grobique/minimal_OPNA_player/minimalOPNA.kicad_sch

## KiCad design minimalOPNA.kicad_sch (2026-03-28)

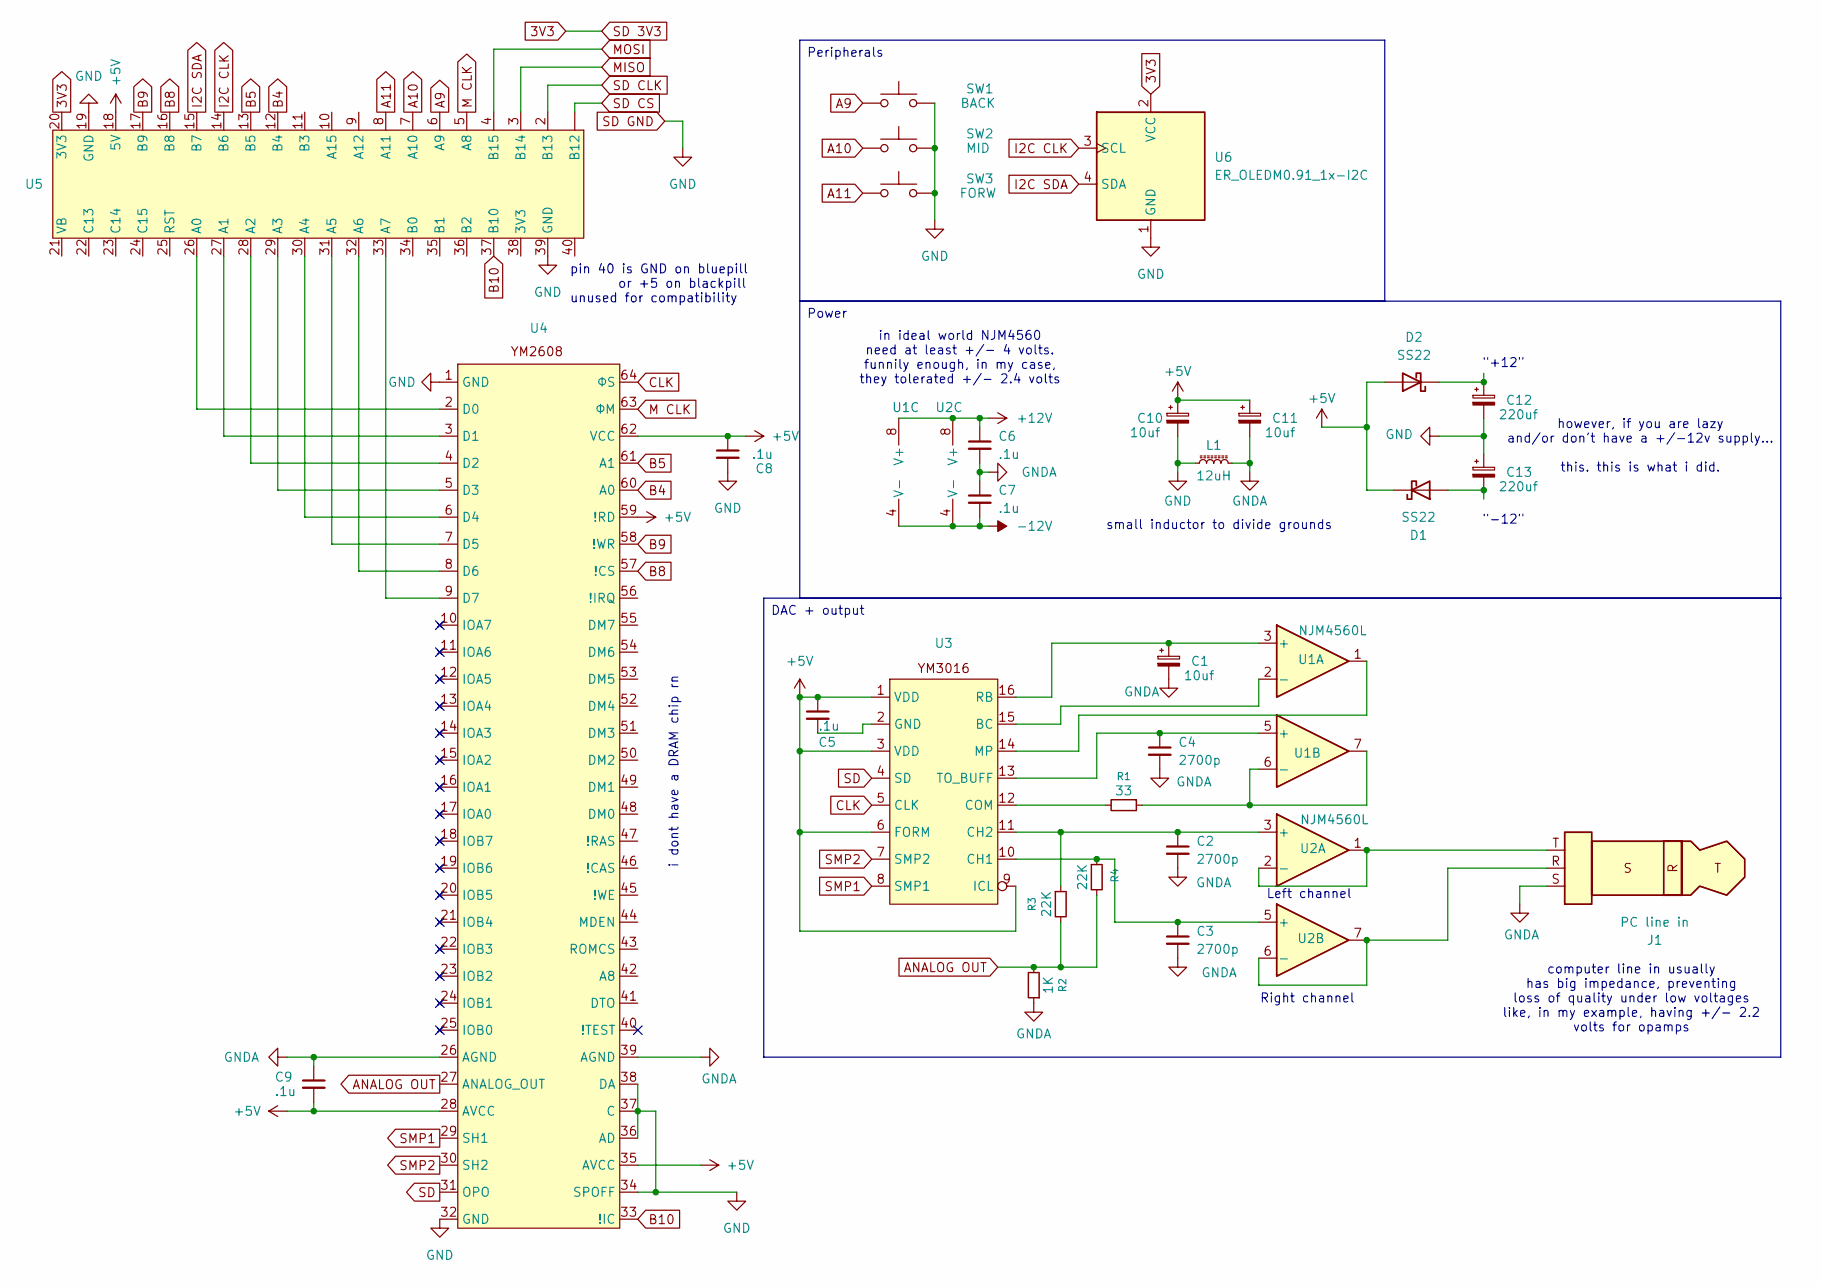
[picture p2: schematic minimalOPNA.kicad_sch]

Parts:
C1, C10, C11: 10uf
C2, C3, C4: 2700p
C5, C6, C7, C8, C9: .1u
C12, C13: 220uf
D1, D2: SS22; D_SMA
J1: PC line in
L1: 12uH
R1: 33
R2: 1K
R3, R4: 22K
SW1: BACK
SW2: MID
SW3: FORW
U1, U2: NJM4560L
U3, U4, U5: (no value)
U6: ER_OLEDM0.91_1x-I2C

Connections:
3V3: U5.20 (3V3), U6.2 (VCC)
+5V: C5.1, C8.1, C9.2, C10.1, C11.1, D1.1 (K), D2.2 (A), U3.1 (VDD), U3.3 (VDD), U3.6 (FORM), U3.9 (ICL), U4.28 (AVCC), U4.35 (AVCC), U4.59 (!RD), U4.62 (VCC), U5.18 (5V)
+12V: C6.1, U1.8 (V+), U2.8 (V+)
-12V: C7.2, U1.4 (V-), U2.4 (V-)
A9: SW1.1, U5.6 (A9)
A10: SW2.1, U5.7 (A10)
A11: SW3.1, U5.8 (A11)
ANALOG OUT: R2.2, R3.2, R4.2, U4.27 (ANALOG_OUT)
B4: U4.60 (A0), U5.12 (B4)
B5: U4.61 (A1), U5.13 (B5)
B8: U4.57 (!CS), U5.16 (B8)
B9: U4.58 (!WR), U5.17 (B9)
B10: U4.33 (!IC), U5.37 (B10)
CLK: U3.5 (CLK), U4.64 (ФS)
GND: C8.2, C10.2, C12.2, C13.1, L1.1, SW1.2, SW2.2, SW3.2, U4.1 (GND), U4.32 (GND), U4.34 (SPOFF), U4.36 (AD), U4.37 (C), U4.38 (DA), U5.19 (GND), U5.39 (GND), U6.1 (GND)
GNDA: C1.2, C2.2, C3.2, C4.2, C6.2, C7.1, C9.1, C11.2, J1.S, L1.2, R2.1, U4.26 (AGND), U4.39 (AGND)
I2C CLK: U5.14 (B6), U6.3 (SCL)
I2C SDA: U5.15 (B7), U6.4 (SDA)
M CLK: U4.63 (ФM), U5.5 (A8)
MISO: U5.3 (B14)
MOSI: U5.4 (B15)
unnamed: C1.1, U1.3 (+), U3.16 (RB)
unnamed: C2.1, R3.1, U2.3 (+), U3.11 (CH2)
unnamed: C3.1, R4.1, U2.5 (+), U3.10 (CH1)
unnamed: C4.1, U1.5 (+), U3.13 (TO_BUFF)
unnamed: C5.2, U3.2 (GND)
unnamed: C12.1, D2.1 (K)
unnamed: C13.2, D1.2 (A)
unnamed: J1.R, U2.6 (-), U2.7
unnamed: J1.T, U2.1, U2.2 (-)
unnamed: R1.1, U1.6 (-), U1.7
unnamed: R1.2, U3.12 (COM)
unnamed: U1.1, U3.14 (MP)
unnamed: U1.2 (-), U3.15 (BC)
unnamed: U4.2 (D0), U5.26 (A0)
unnamed: U4.3 (D1), U5.27 (A1)
unnamed: U4.4 (D2), U5.28 (A2)
unnamed: U4.5 (D3), U5.29 (A3)
unnamed: U4.6 (D4), U5.30 (A4)
unnamed: U4.7 (D5), U5.31 (A5)
unnamed: U4.8 (D6), U5.32 (A6)
unnamed: U4.9 (D7), U5.33 (A7)
SD: U3.4 (SD), U4.31 (OPO)
SD CLK: U5.2 (B13)
SD CS: U5. (B12)
SMP1: U3.8 (SMP1), U4.29 (SH1)
SMP2: U3.7 (SMP2), U4.30 (SH2)

Notes on the sheet:
however, if you are lazy and/or don't have a +/-12v supply... this. this is what i did.
i dont have a DRAM chip rn
in ideal world NJM4560 need at least +/- 4 volts. funnily enough, in my case, they tolerated +/- 2.4 volts
small inductor to divide grounds
Left channel
"-12"
computer line in usually has big impedance, preventing loss of quality under low voltages like, in my example, having +/- 2.2 volts for opamps
pin 40 is GND on bluepill or +5 on blackpill unused for compatibility
"+12"
Right channel
DAC + output
Peripherals
Power
